awasson/AVI-ELF-II/notes/ASCII-KEYBOARD/ASCII-Keyboard-Image.png

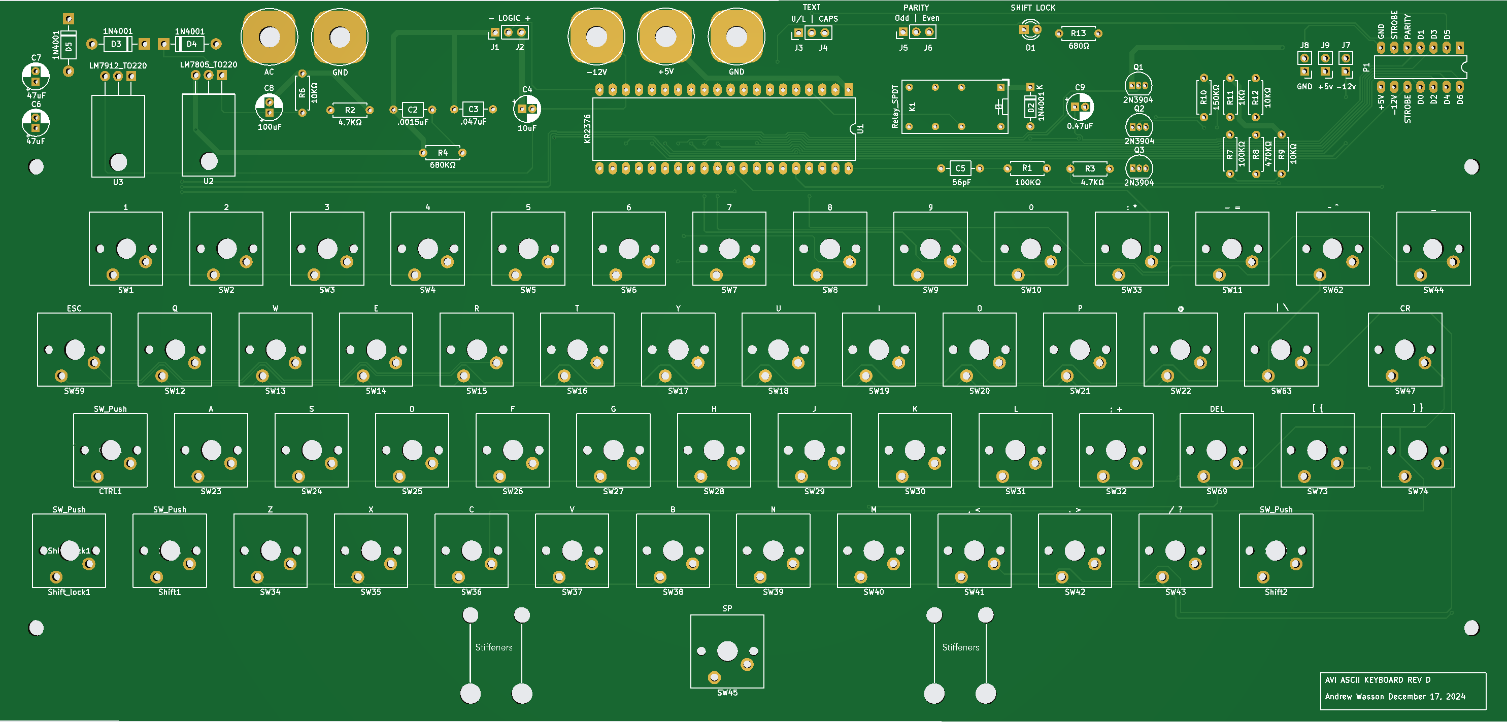
notes/ASCII-KEYBOARD/ASCII-Keyboard-Image.png
