awasson/AVI-ELF-II/notes/ASCII-KEYBOARD/AVI ASCII Keyboard Rev D.png

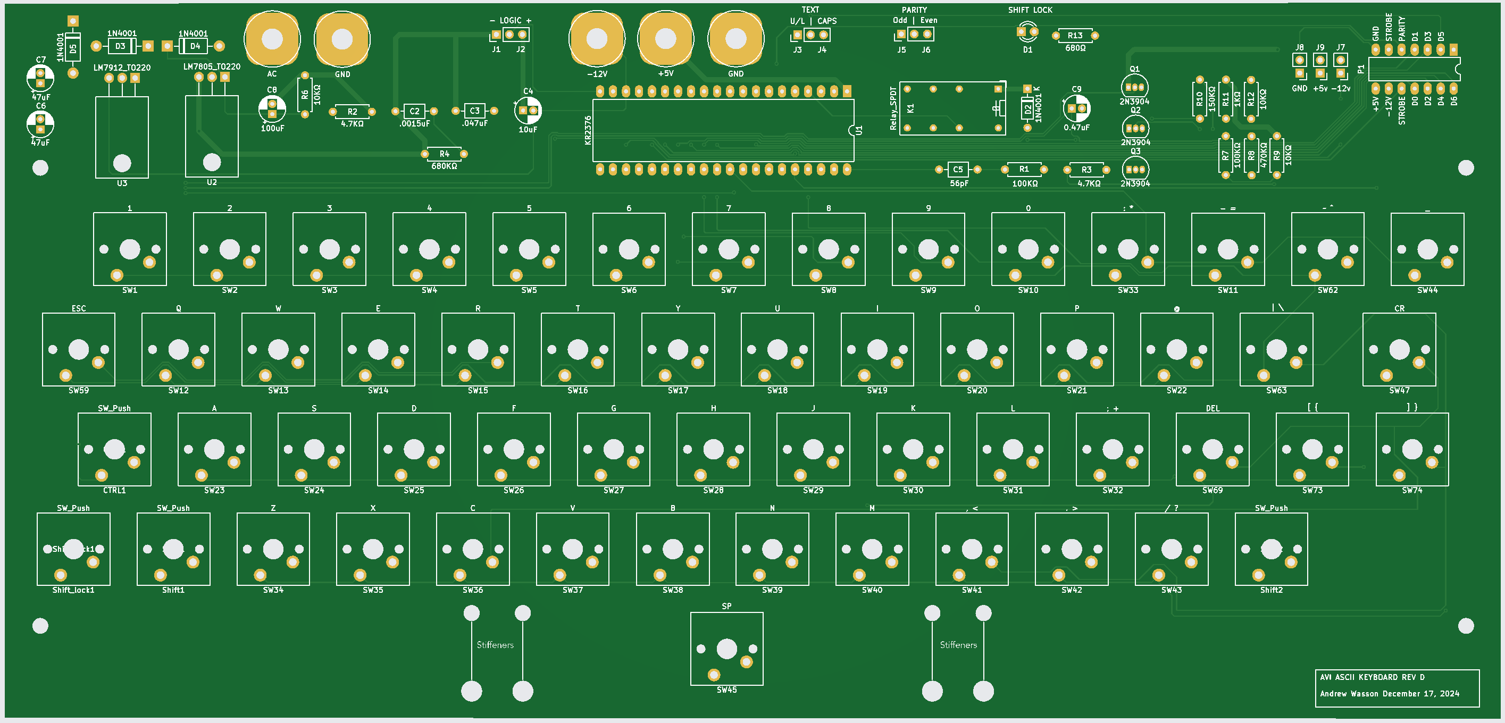
notes/ASCII-KEYBOARD/AVI ASCII Keyboard Rev D.png
