awasson/AVI-ELF-II/notes/ASCII-KEYBOARD/IMG_1968.jpeg

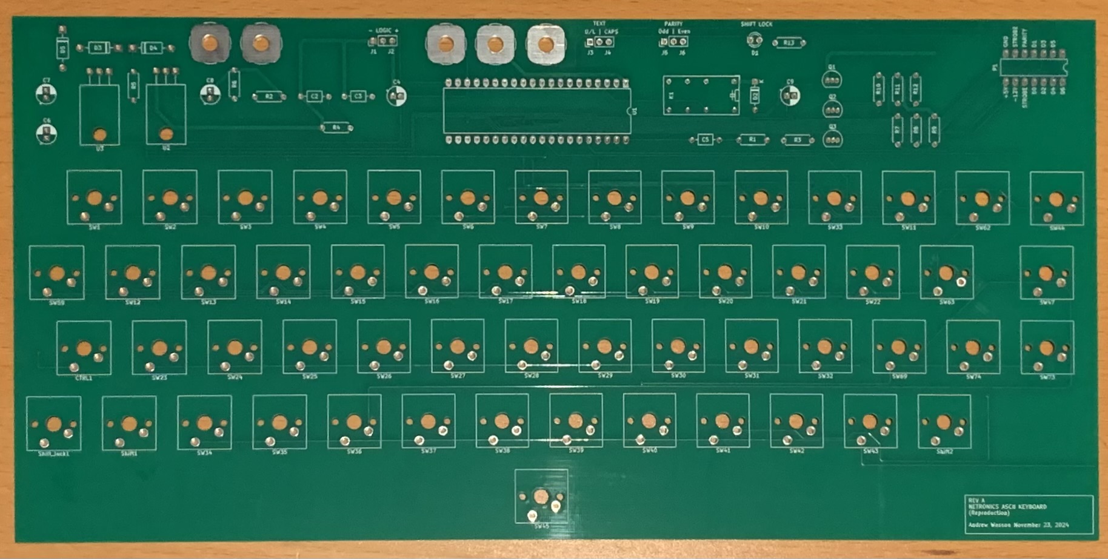
notes/ASCII-KEYBOARD/IMG_1968.jpeg
