awasson/AVI-ELF-II/notes/AVIELF2-VIP/AVIELF2-VIP.jpg

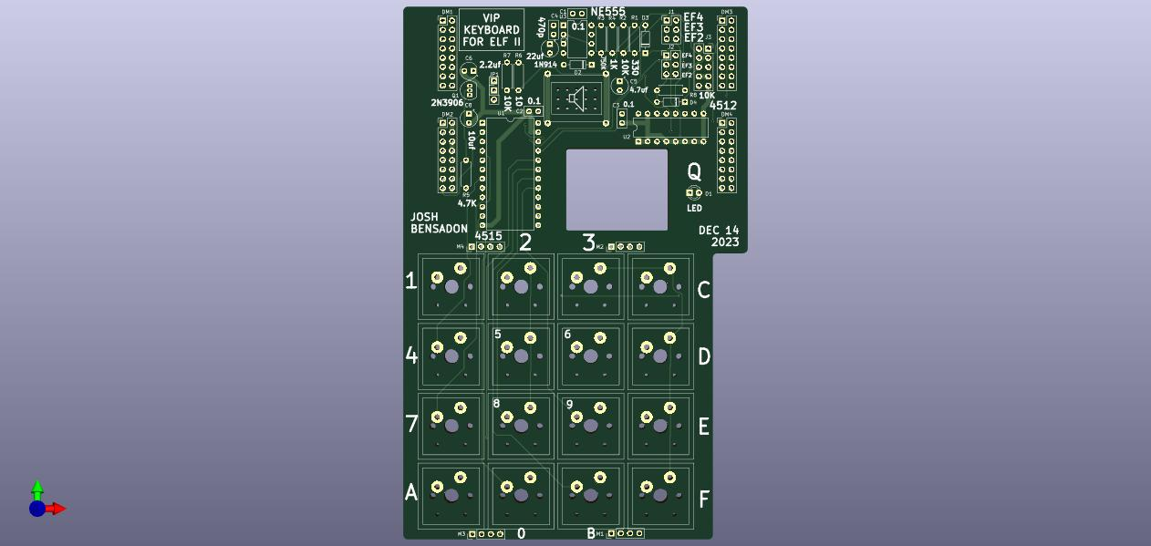
notes/AVIELF2-VIP/AVIELF2-VIP.jpg
