awasson/AVI-ELF-II/notes/AVIELF2DISPLAYMAX7219/AVIELF2DISPLAYMAX7219.jpg

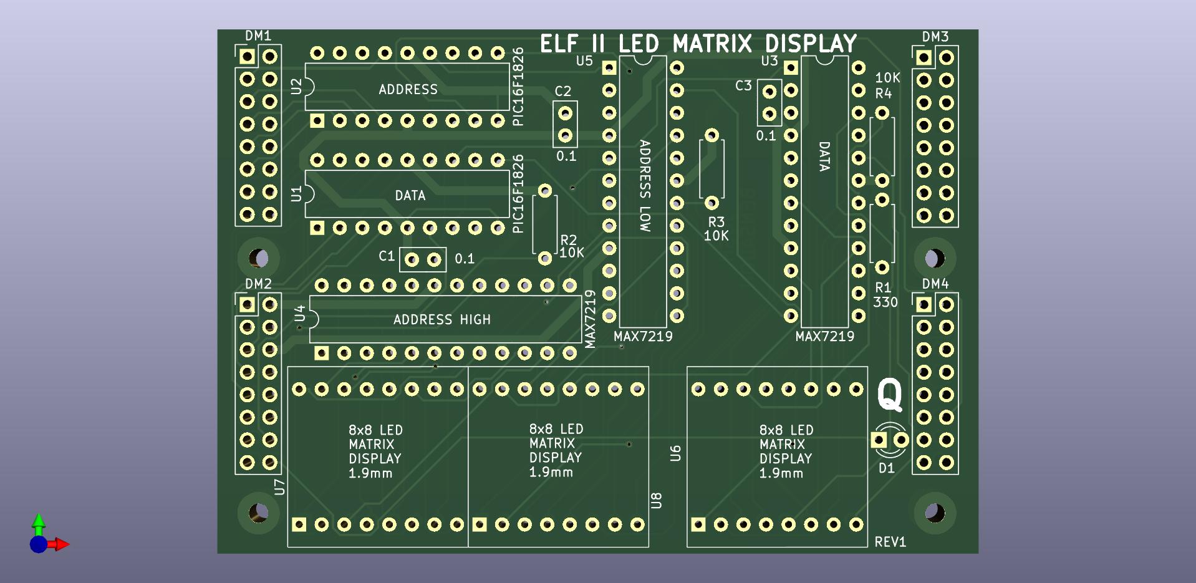
notes/AVIELF2DISPLAYMAX7219/AVIELF2DISPLAYMAX7219.jpg
