awasson/AVI-ELF-II/notes/AVIELF2KEYBOARD/AVIELF2KEYBOARD.jpg

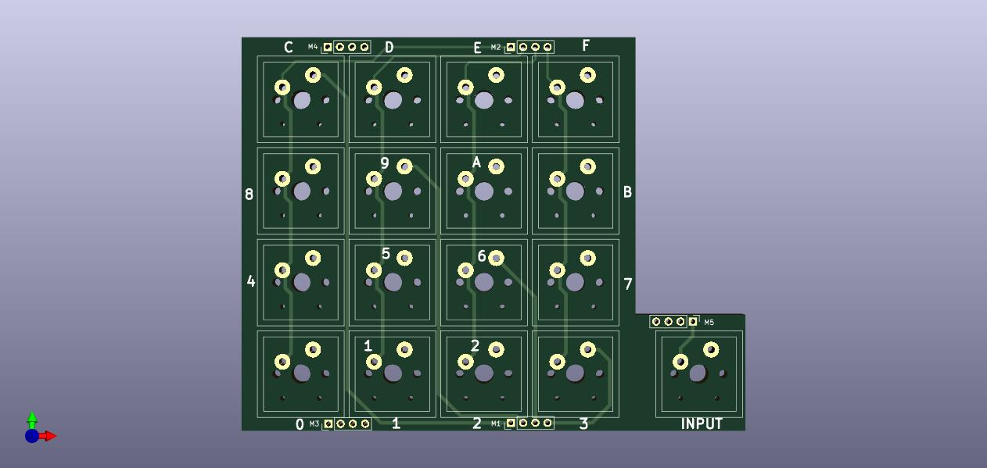
notes/AVIELF2KEYBOARD/AVIELF2KEYBOARD.jpg
