awasson/AVI-ELF-II/notes/AVIELF2Prototyping/AVIELF2Prototyping.jpg

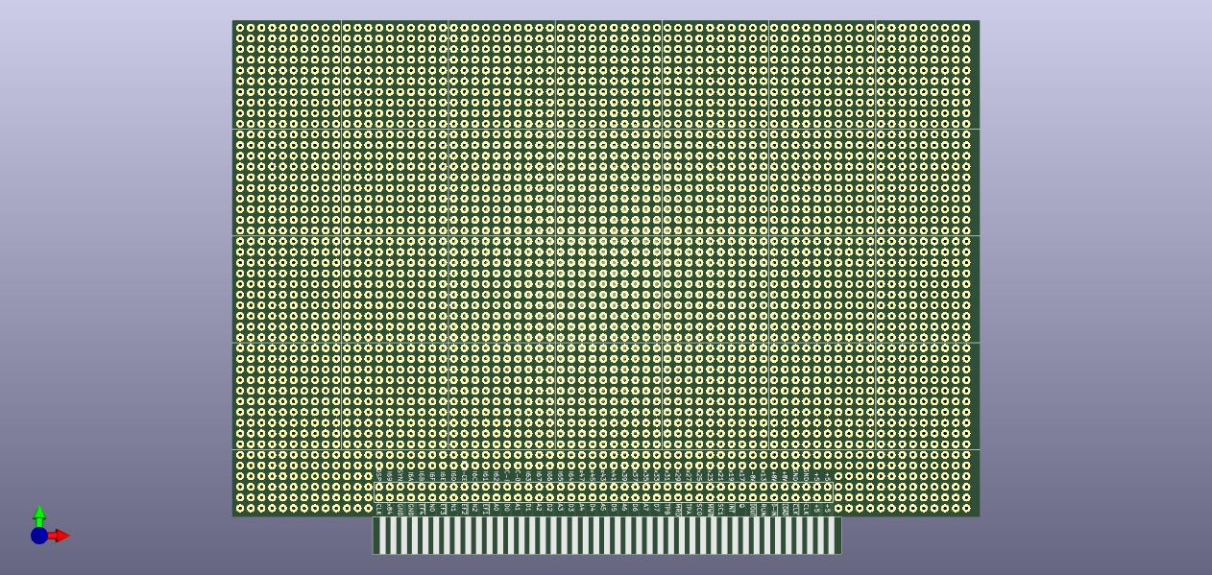
notes/AVIELF2Prototyping/AVIELF2Prototyping.jpg
