awasson/AVI-ELF-II/notes/AVIELF2SD/AVIELF2SD.jpg

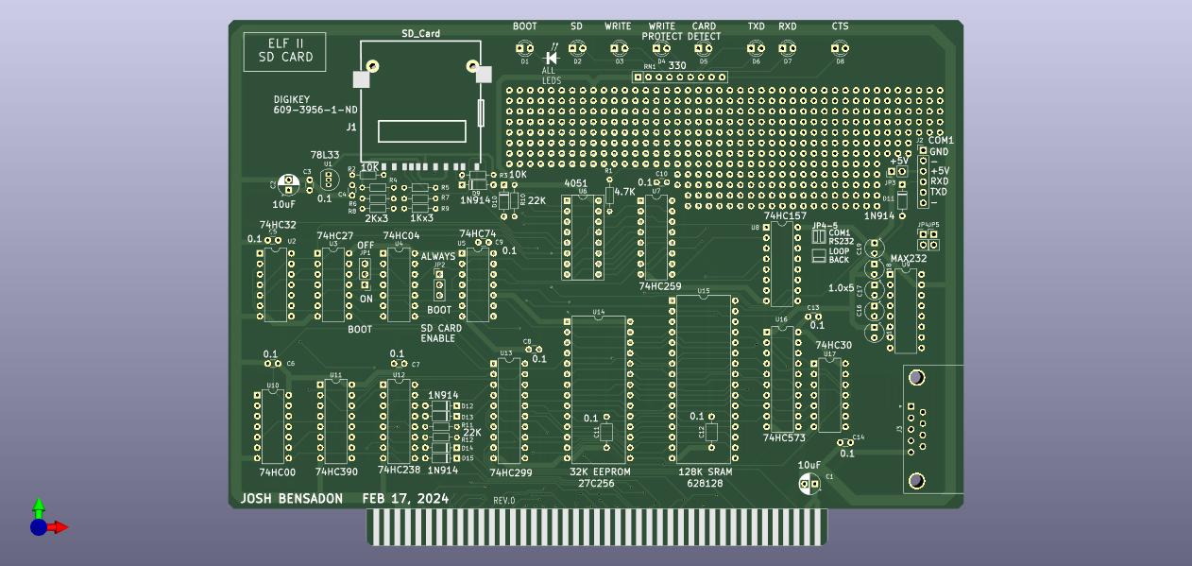
notes/AVIELF2SD/AVIELF2SD.jpg
