awasson/AVI-ELF-II/notes/AVIELFSTGDISK0/AVIELFSTGDISK0.jpg

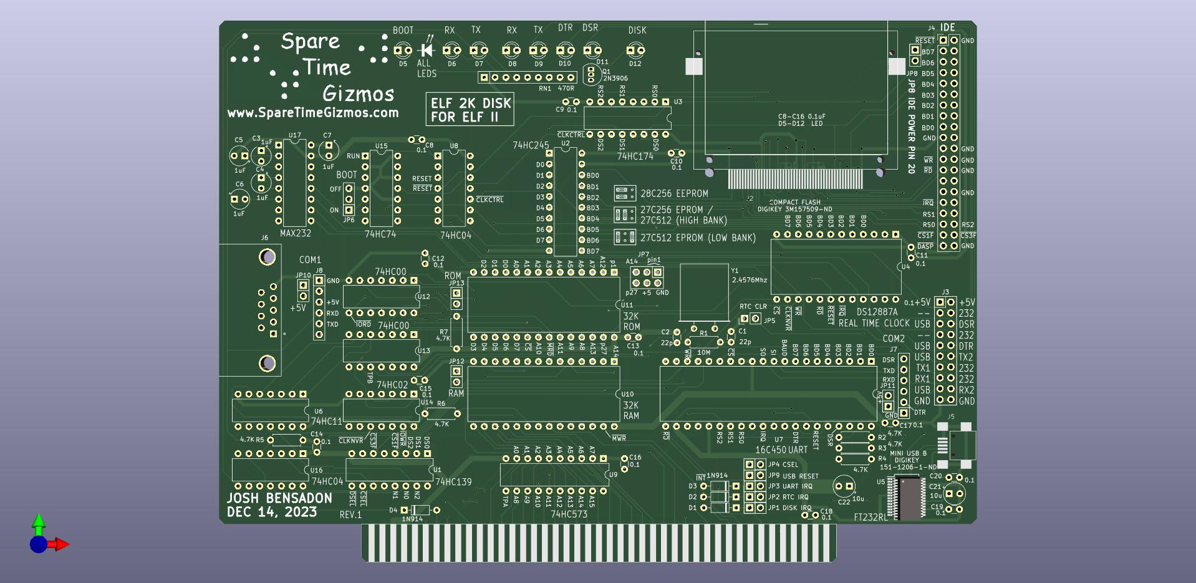
notes/AVIELFSTGDISK0/AVIELFSTGDISK0.jpg
