awasson/AVI-ELF-II/notes/ELF-II/AVIELF2v1.jpg

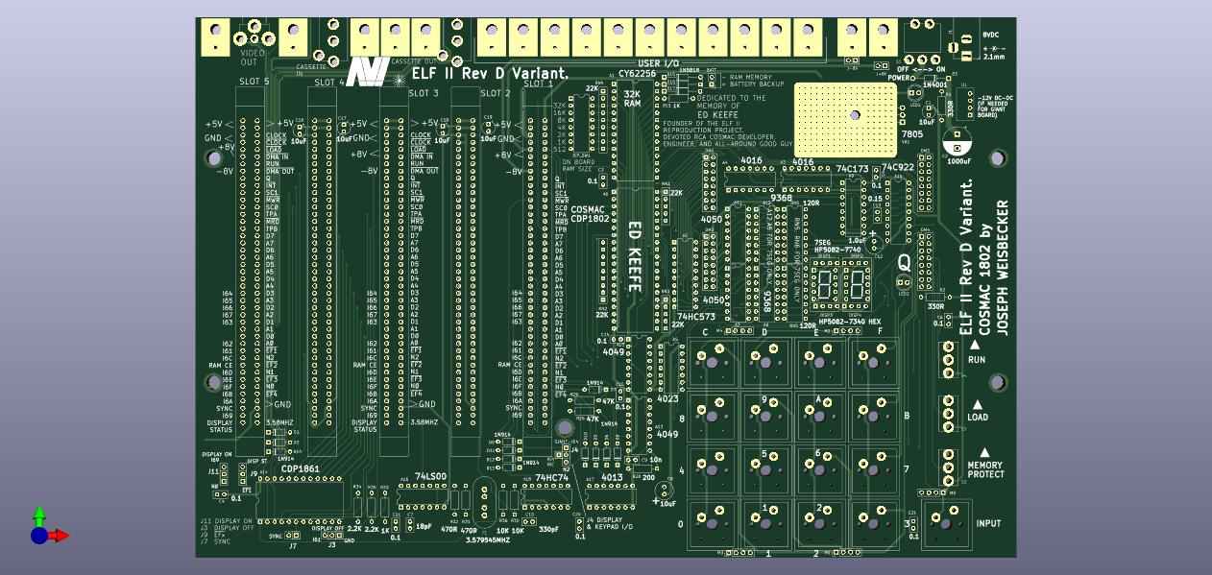
notes/ELF-II/AVIELF2v1.jpg
