awasson/AVI-ELF-II/notes/Hyperboard/AVIELF2HYPERBOARD.jpg

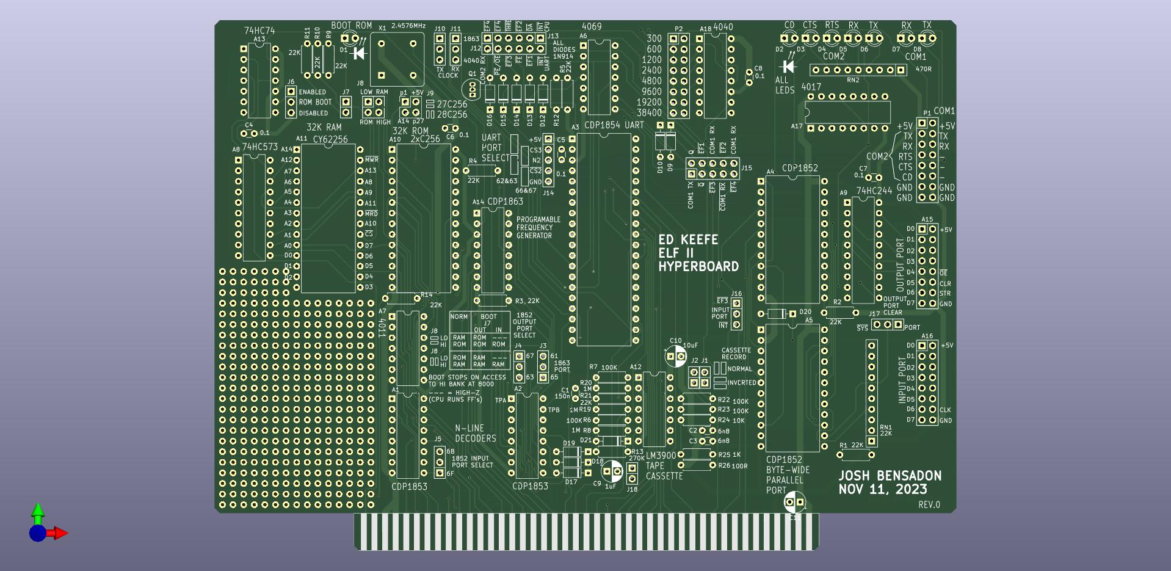
notes/Hyperboard/AVIELF2HYPERBOARD.jpg
