awasson/AVI-ELF-II/notes/TIL311-6DIGIT-DISPLAY/AVI ELF II TIL311 6-Digit Display Card.png

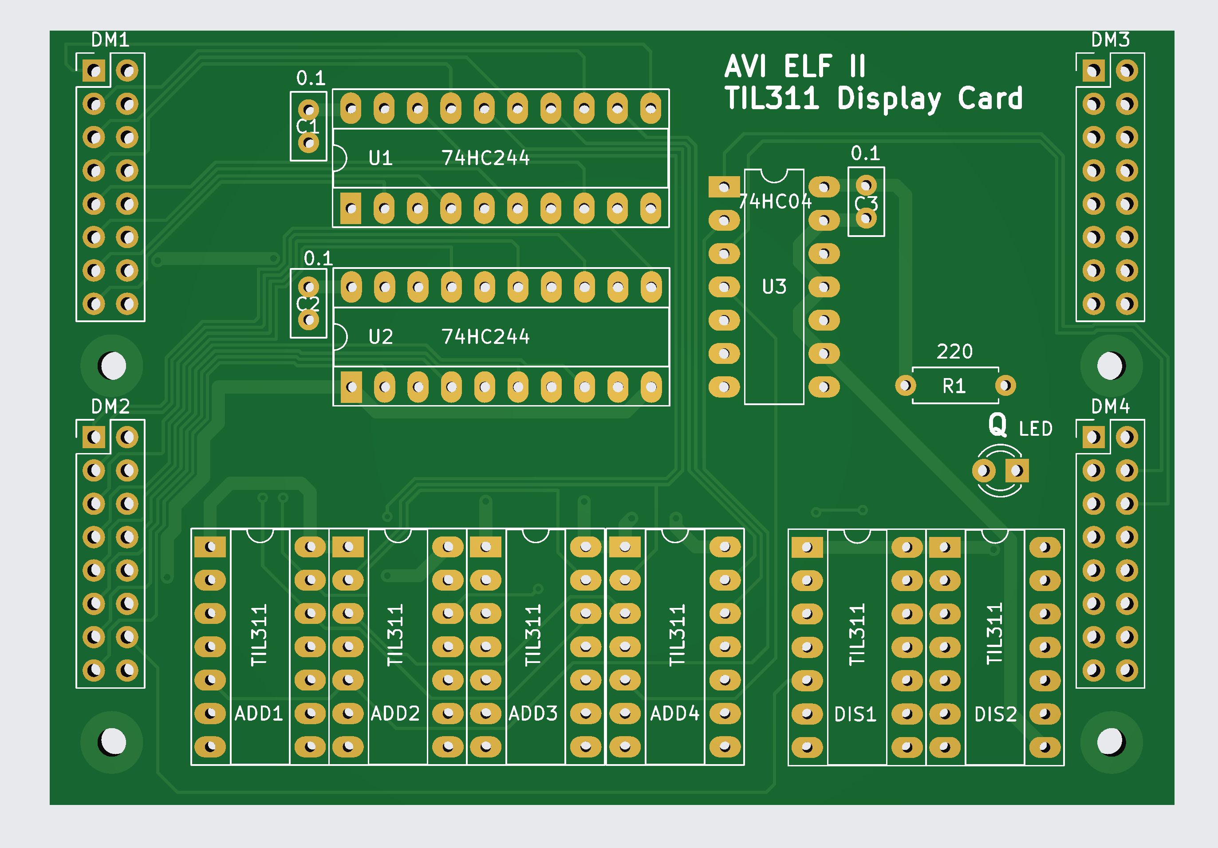
notes/TIL311-6DIGIT-DISPLAY/AVI ELF II TIL311 6-Digit Display Card.png
