awasson/AVI-ELF-II/photos/image_6487327.JPG

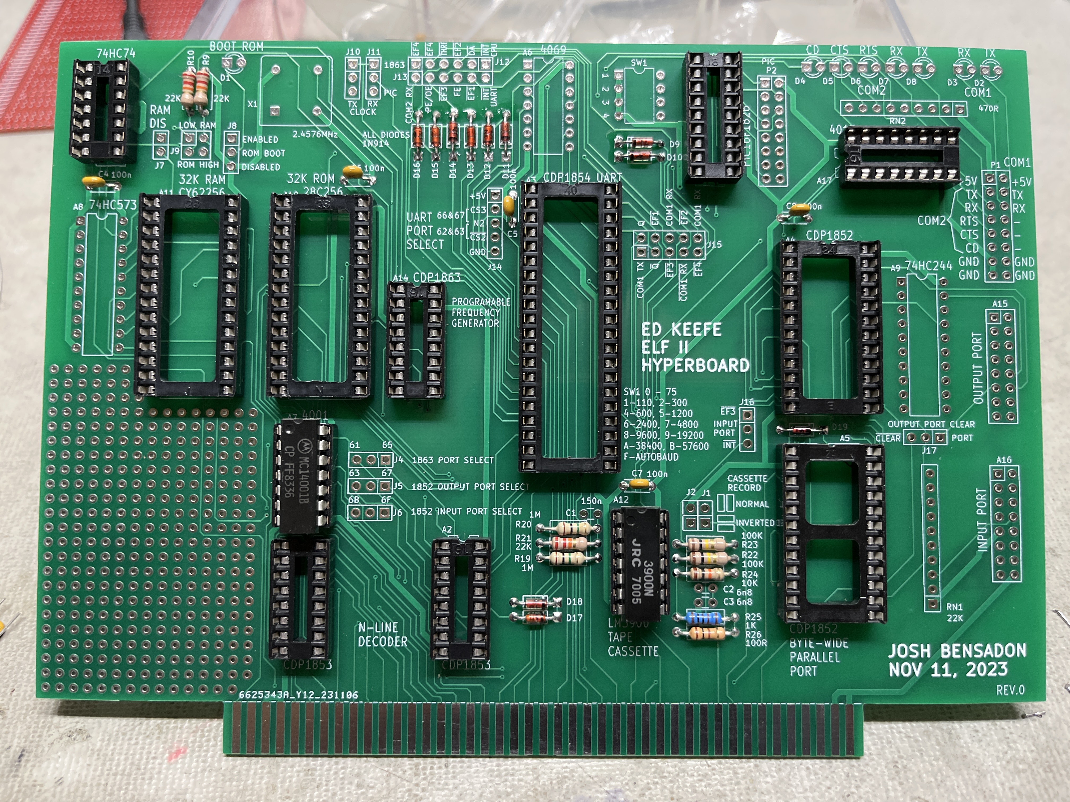
photos/image_6487327.JPG
