awasson/AVI-ELF-II/photos/IMG_0209.jpeg

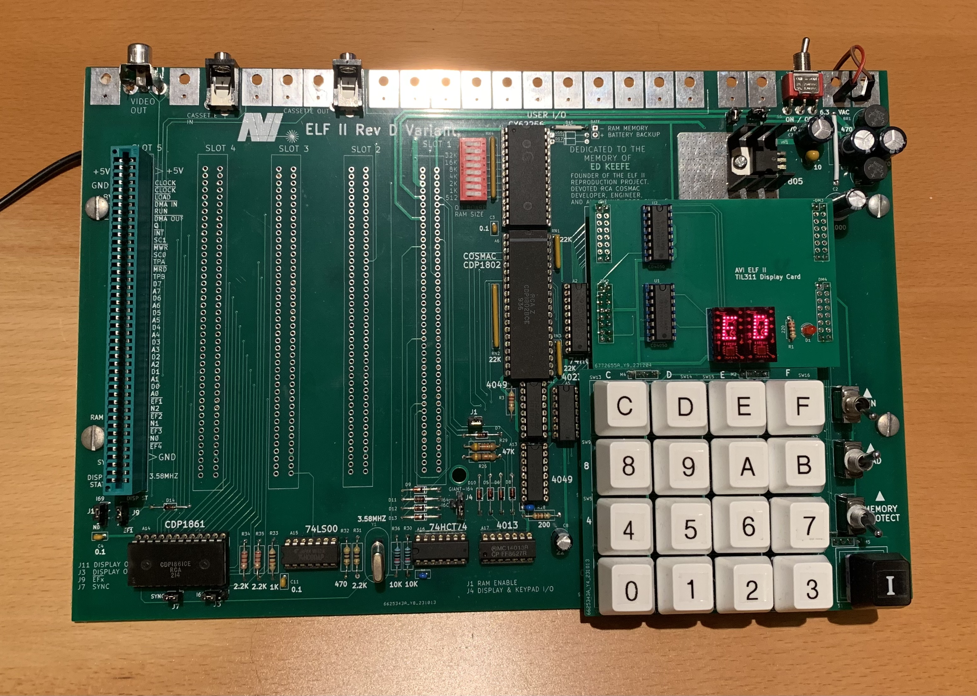
photos/IMG_0209.jpeg
