awasson/AVI-ELF-II/photos/IMG_3701.jpeg

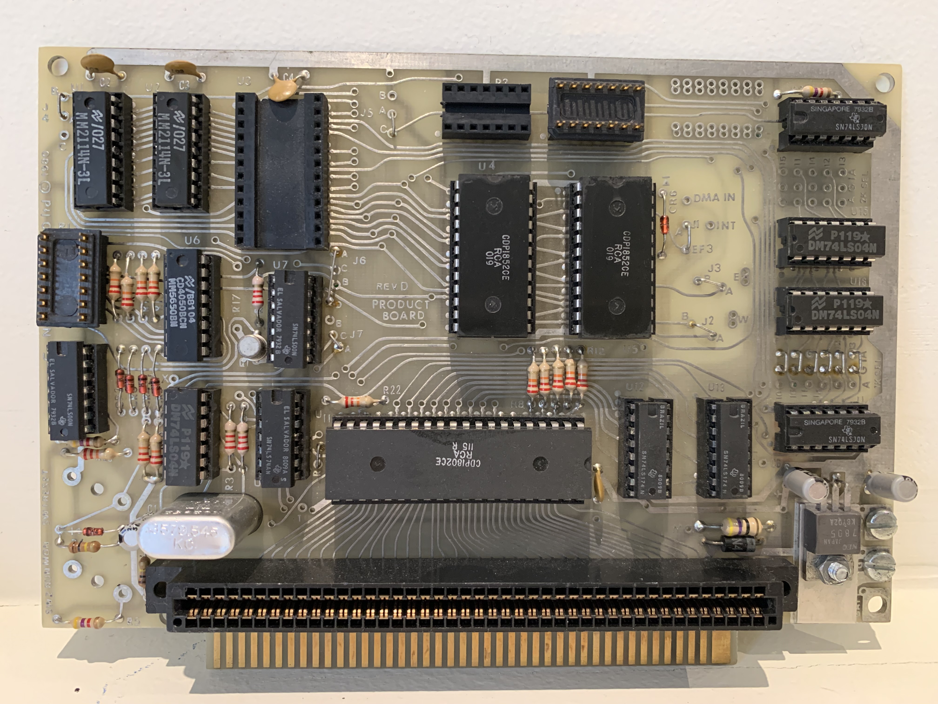
photos/IMG_3701.jpeg
