awasson/AVI-ELF-II/photos/IMG_3702.jpeg

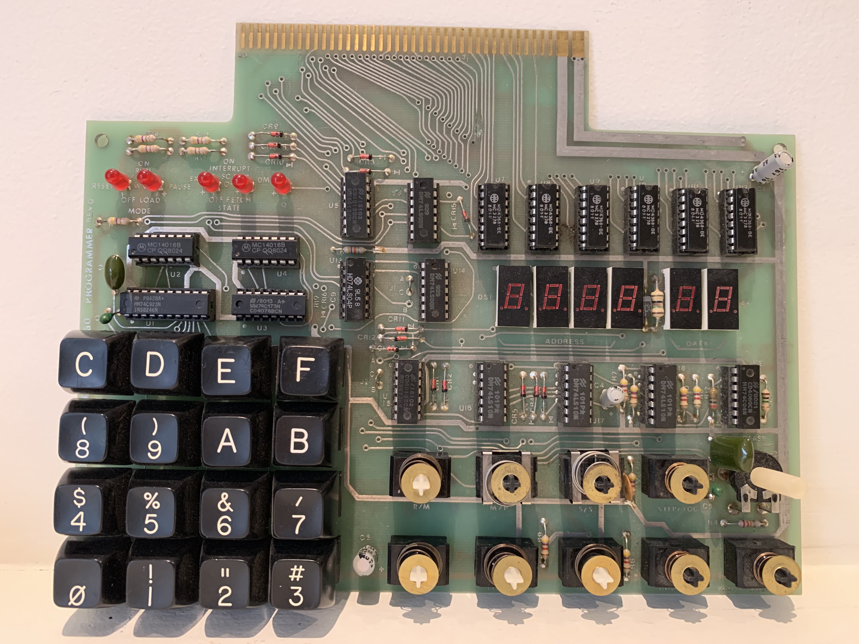
photos/IMG_3702.jpeg
