awasson/AVI-ELF-II/photos/IMG_9843.jpeg

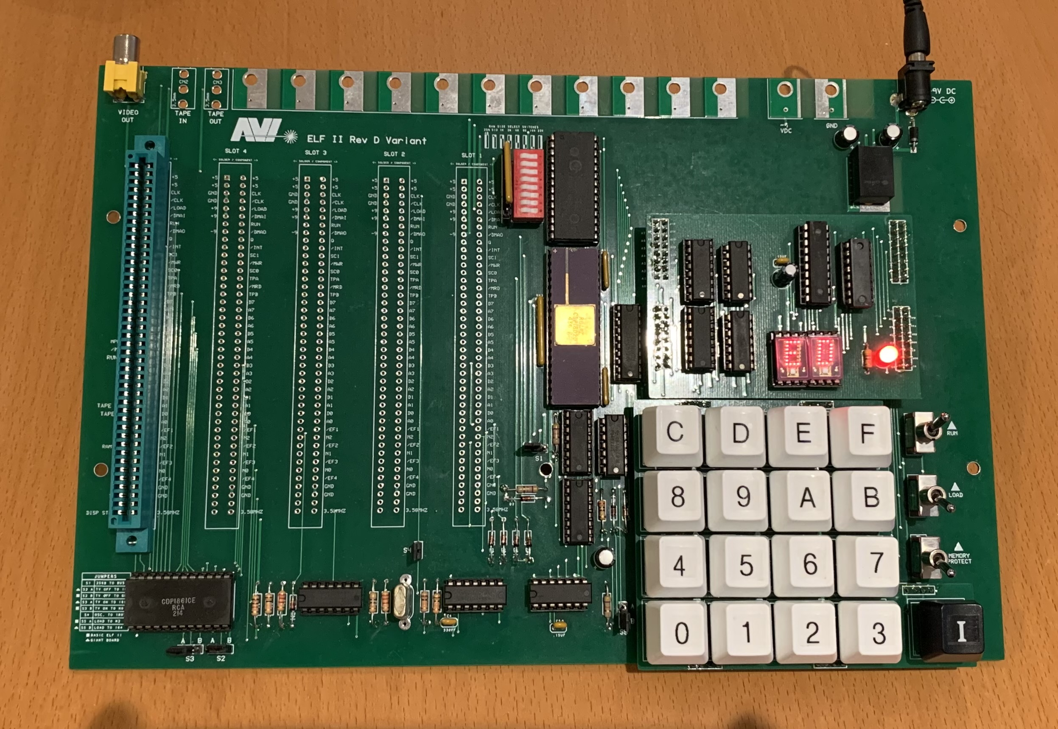
photos/IMG_9843.jpeg
