awasson/AVI-ELF-II/photos/IMG_9854.jpeg

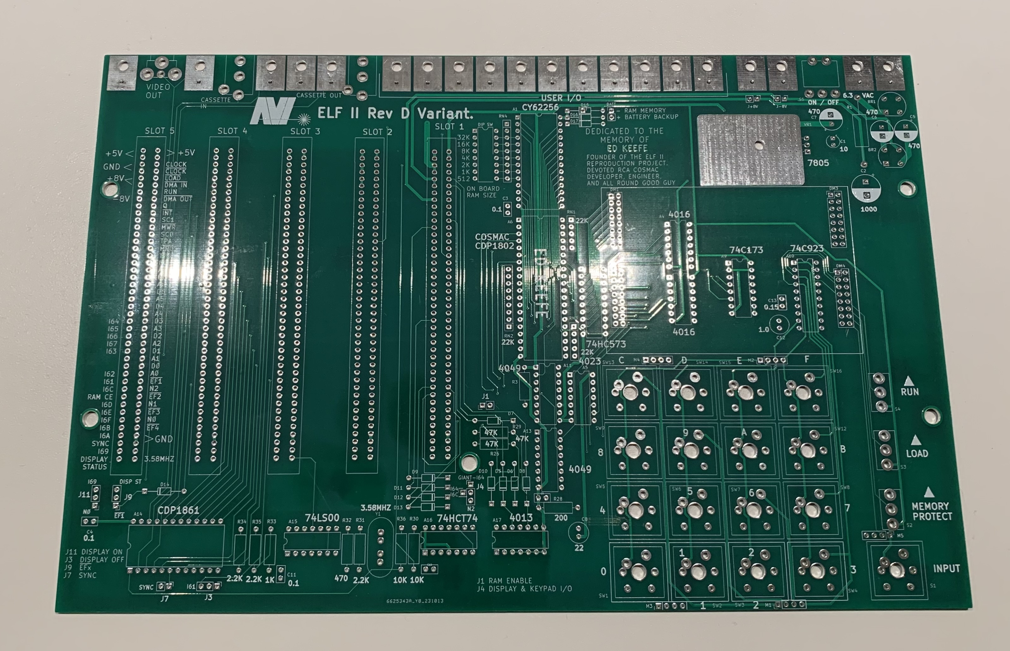
photos/IMG_9854.jpeg
