awasson/AVI-ELF-II/notes/AVIELF2DISPLAYMAX7219/AVIELF2DISPLAYMAX7219.xlsx

Sheet: Digikey.ca
QTY | PART # | PART | DESCRIPTION | NOTES | DIGIKEY
IC's
2 | U1, U2 | PIC16F1826 | 16F Microcontroller IC 8-Bit 32MHz | 16F Microcontroller IC 8-Bit 32MHz | https://www.digikey.ca/en/products/detail/microchip-technology/PIC16F1826-I-P/2201960
3 | U3, U4, U5 | MAX7219 | MAX7219 8-Digit LED Display Drivers | Amazon.ca sells these in a pack of 10: https://www.amazon.ca/gp/product/B09P47ZW8L
 |  |  |  | Amazon.com sells these in lots of 5: https://www.amazon.com/Bridgold-MAX7219CNG-MAX7219-Serially-Interfaced/dp/B0BK6XC4P8/r
LED's
3 | U6, U7, U8 | 8x8 LED Dot Matrix Display | 8x8 Dot Matrix Led Lattice Red Display Module 1.9mm | Can be found at AliExpress: https://www.aliexpress.com/item/4000931195417.html
1 | D1 | /Q LED | 3.0mm Red LED | Dialight appears to have suitable LED's in 3mm | https://www.digikey.ca/en/products/filter/led-indication-discrete/105
Resistors
1 | R1 | 330 | 330 Ohms Carbon Film Resistor |  | https://www.digikey.ca/en/products/detail/stackpole-electronics-inc/CF14JT330R/1741399
1 | R2, R3, R4 | 10K | 10 kOhms Carbon Film Resistor |  | https://www.digikey.ca/en/products/detail/stackpole-electronics-inc/CF14JT10K0/1741265
Capacitors
3 | C1, C2, C3 | 0.1uf | 0.1uf Ceramic Capacitor |  | https://www.digikey.ca/en/products/detail/kemet/C320C104K5R5TA7317/6562447
4 | DM1, DM2, DM3, DM4 | Dual row header strip | Connector Header Through Hole 80 position 0.100" (2.54mm) | Cut strip to number of conductors required | https://www.digikey.ca/en/products/detail/adam-tech/PH2-80-UA/9830504

Sheet: Digikey.com
QTY | PART # | PART | DESCRIPTION | NOTES | DIGIKEY
IC's
2 | U1, U2 | PIC16F1826 | 16F Microcontroller IC 8-Bit 32MHz | 16F Microcontroller IC 8-Bit 32MHz | https://www.digikey.com/en/products/detail/microchip-technology/PIC16F1826-I-P/2201960 (https://www.digikey.ca/en/products/detail/microchip-technology/PIC16F1826-I-P/2201960)
3 | U3, U4, U5 | MAX7219 | MAX7219 8-Digit LED Display Drivers | Amazon.ca sells these in a pack of 10: https://www.amazon.ca/gp/product/B09P47ZW8L
 |  |  |  | Amazon.com sells these in lots of 5: https://www.amazon.com/Bridgold-MAX7219CNG-MAX7219-Serially-Interfaced/dp/B0BK6XC4P8/r
LED's
3 | U6, U7, U8 | 8x8 LED Dot Matrix Display | 8x8 Dot Matrix Led Lattice Red Display Module 1.9mm | Can be found at AliExpress: https://www.aliexpress.com/item/4000931195417.html
1 | D1 | /Q LED | 3.0mm Red LED | Dialight appears to have suitable LED's in 3mm | https://www.digikey.com/en/products/filter/led-indication-discrete/105 (https://www.digikey.ca/en/products/filter/led-indication-discrete/105)
Resistors
1 | R1 | 330 | 330 Ohms Carbon Film Resistor |  | https://www.digikey.com/en/products/detail/stackpole-electronics-inc/CF14JT330R/1741399 (https://www.digikey.ca/en/products/detail/stackpole-electronics-inc/CF14JT330R/1741399)
1 | R2, R3, R4 | 10K | 10 kOhms Carbon Film Resistor |  | https://www.digikey.com/en/products/detail/stackpole-electronics-inc/CF14JT10K0/1741265 (https://www.digikey.ca/en/products/detail/stackpole-electronics-inc/CF14JT10K0/1741265)
Capacitors
3 | C1, C2, C3 | 0.1uf | 0.1uf Ceramic Capacitor |  | https://www.digikey.com/en/products/detail/kemet/C320C104K5R5TA7317/6562447 (https://www.digikey.ca/en/products/detail/kemet/C320C104K5R5TA7317/6562447)
4 | DM1, DM2, DM3, DM4 | Dual row header strip | Connector Header Through Hole 80 position 0.100" (2.54mm) | Cut strip to number of conductors required | https://www.digikey.com/en/products/detail/adam-tech/PH2-80-UA/9830504 (https://www.digikey.ca/en/products/detail/adam-tech/PH2-80-UA/9830504)
