awasson/AVI-ELF-II/notes/Hyperboard-Rev-2/AVIELF2HYPERBOARD-KiCad-Rev2.pdf

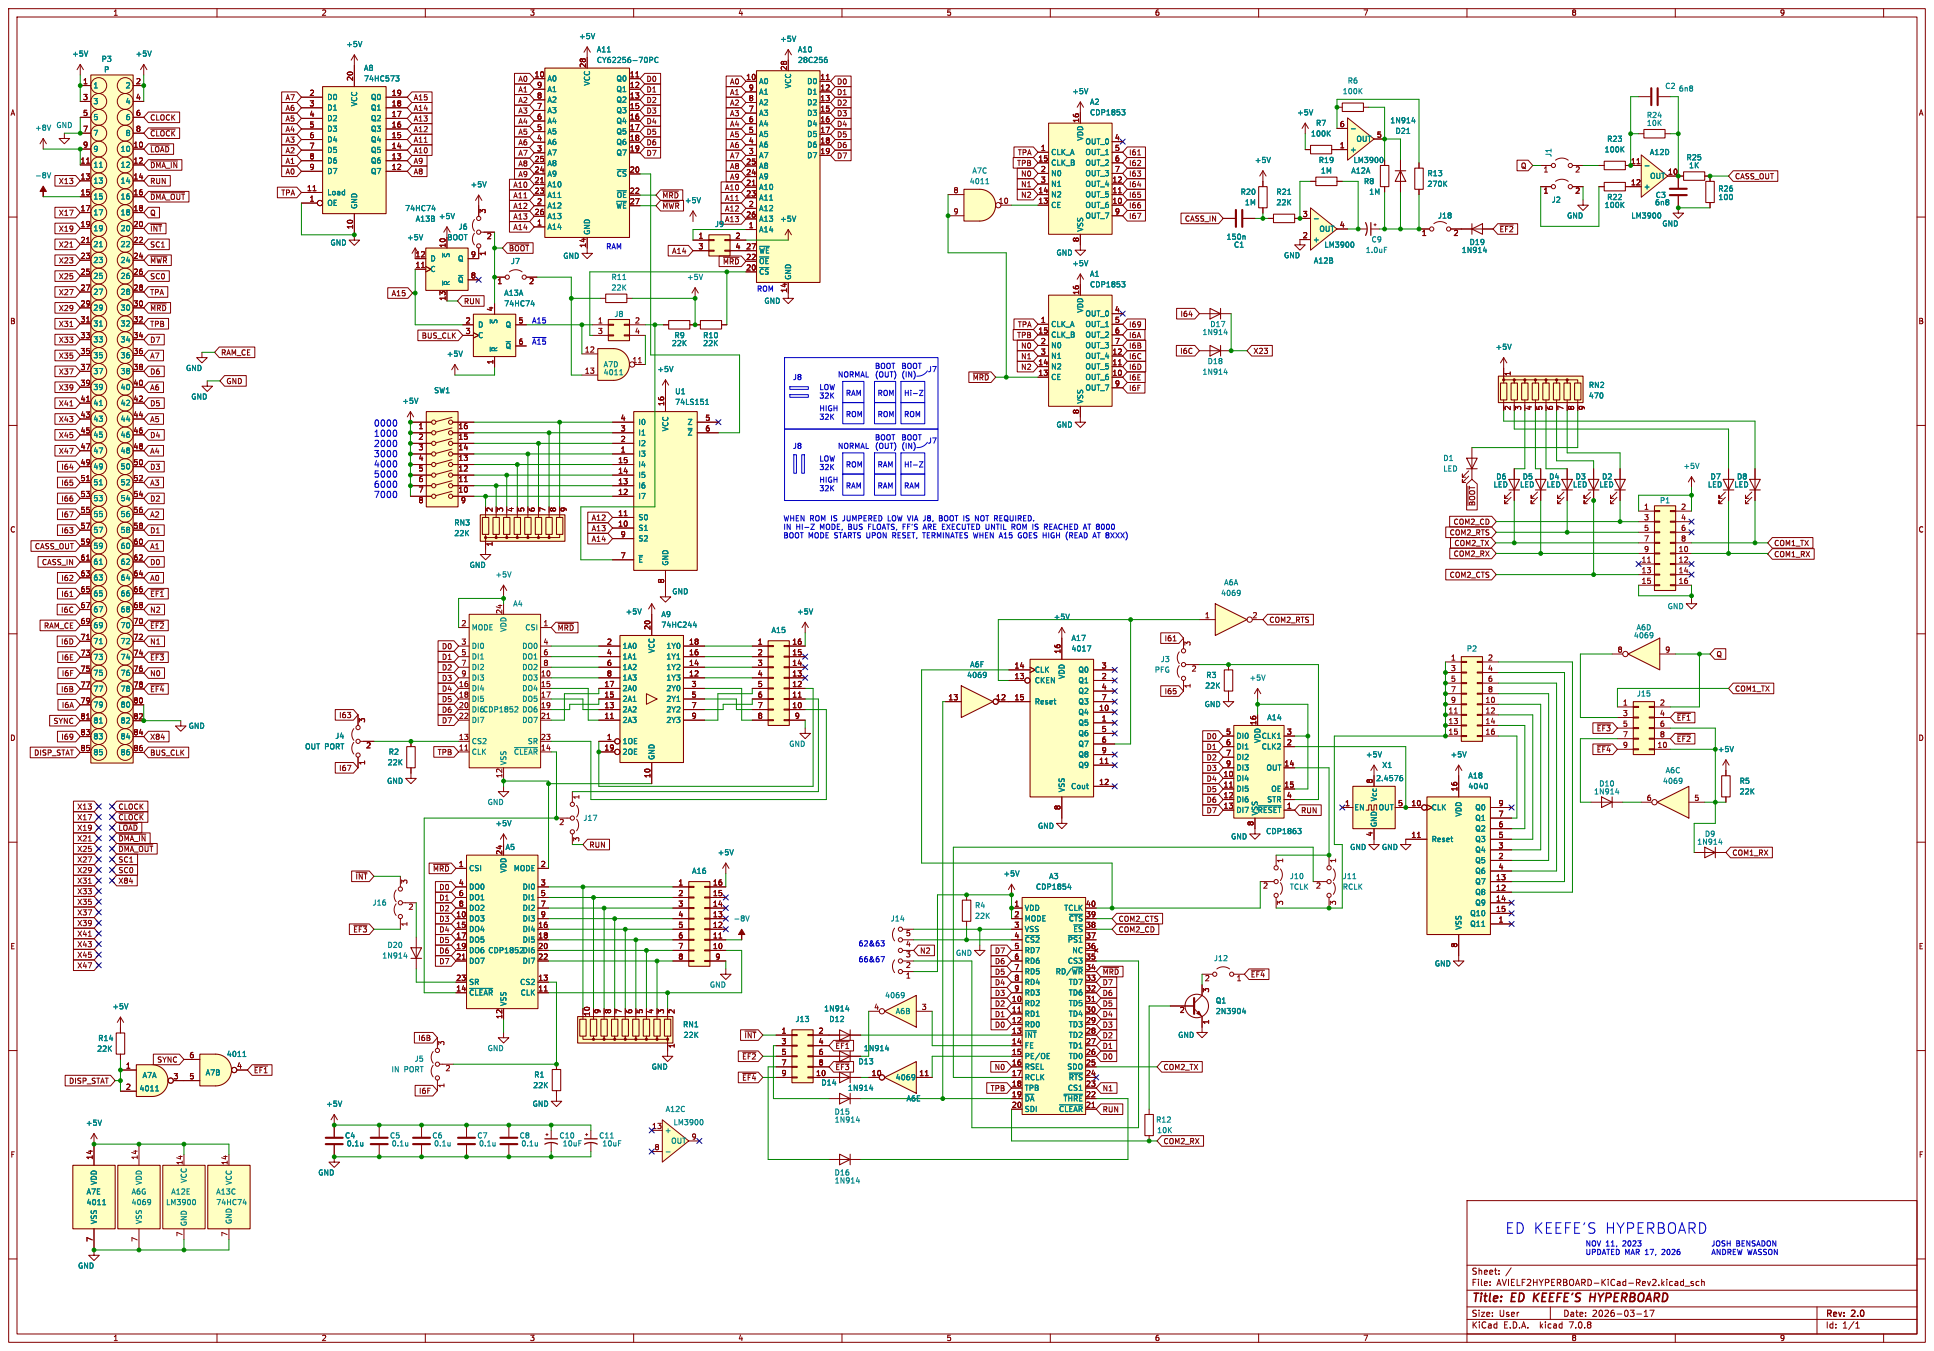
[picture p46: page 1]

IN HI-Z MODE, BUS FLOATS, FF'S ARE EXECUTED UNTIL ROM IS REACHED AT 8000 BOOT MODE STARTS UPON RESET, TERMINATES WHEN A15 GOES HIGH (READ AT 8XXX) ROM

(IN) WHEN ROM IS JUMPERED LOW VIA J8, BOOT IS NOT REQUIRED.

8 Q8 9 A14 CDP1863 ~{RESET}1 DI4 10 DI5 11 DI6 12 DI7 13 OUT 14 OE 15 VDD 16 CLK2 2 CLK1 3 STR 4 DI0 5 DI1 6 DI2 7 VSS

File: AVIELF2HYPERBOARD-KiCad-Rev2.kicad_sch Sheet: /
Id: 1/1 Title: ED KEEFE'S HYPERBOARD
