awasson/AVI-ELF-II/photos/image_123927839.JPG

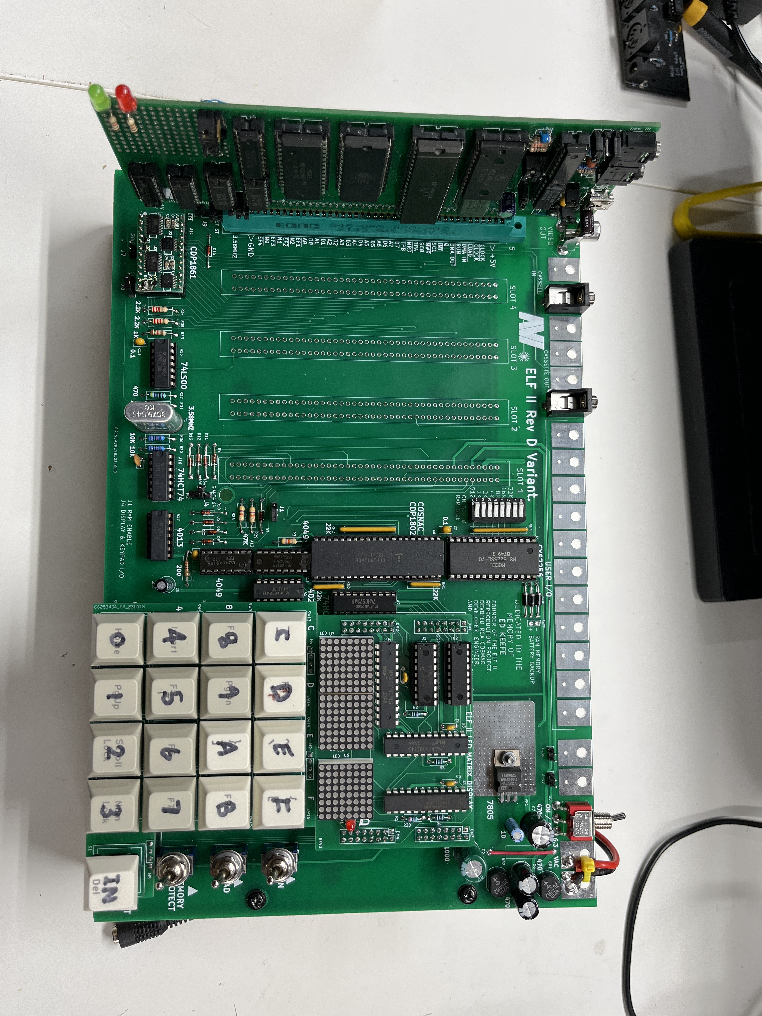
photos/image_123927839.JPG
